SergTyapkin/Compass-Minecraft-ESP32/firmware/src/clocks.h

#pragma once
#include "pixel.h"

#define CL_BLUE 0     // Светлое небо
#define CL_BLUE_D 1   // Темное небо
#define CL_YELLOW 2   // Светлая часть стрелки солнца
#define CL_YELLOW_D 3 // Темная часть стрелки солнца
#define CL_WHITE 4    // Светлая часть стрелки луны
#define CL_WHITE_D 5  // Темная часть стрелки луны

static const Pix CL_0[] = {
    {CL_WHITE, 11},
    {CL_WHITE, 19},
    {CL_WHITE, 27},
    {CL_WHITE, 35},
    {CL_WHITE, 43},
    {CL_WHITE_D, 18},
    {CL_WHITE_D, 10},
    {CL_WHITE_D, 3},
    {CL_WHITE_D, 12},
    {CL_WHITE_D, 20},
    {CL_BLUE, 48},
    {CL_BLUE, 49},
    {CL_BLUE, 50},
    {CL_BLUE, 51},
    {CL_BLUE, 52},
    {CL_BLUE, 53},
    {CL_BLUE, 54},
    {CL_BLUE_D, 40},
    {CL_BLUE_D, 41},
    {CL_BLUE_D, 42},
    {CL_BLUE_D, 44},
    {CL_BLUE_D, 45},
    {CL_BLUE_D, 46},
};
static const Pix CL_1[] = {
    {CL_WHITE, 12},
    {CL_WHITE, 20},
    {CL_WHITE, 28},
    {CL_WHITE, 35},
    {CL_WHITE, 43},
    {CL_WHITE_D, 27},
    {CL_WHITE_D, 19},
    {CL_WHITE_D, 11},
    {CL_WHITE_D, 4},
    {CL_WHITE_D, 13},
    {CL_WHITE_D, 21},
    {CL_BLUE, 40},
    {CL_BLUE, 48},
    {CL_BLUE, 49},
    {CL_BLUE, 50},
    {CL_BLUE, 51},
    {CL_BLUE, 52},
    {CL_BLUE, 53},
    {CL_BLUE_D, 32},
    {CL_BLUE_D, 41},
    {CL_BLUE_D, 42},
    {CL_BLUE_D, 44},
    {CL_BLUE_D, 45},
    {CL_BLUE_D, 54},
};
static const Pix CL_2[] = {
    {CL_WHITE, 21},
    {CL_WHITE, 28},
    {CL_WHITE, 36},
    {CL_WHITE, 43},
    {CL_WHITE_D, 20},
    {CL_WHITE_D, 13},
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
    sizeof(CL_23),
    sizeof(CL_24),
    sizeof(CL_25),
    sizeof(CL_26),
    sizeof(CL_27),
};

uint8_t getClockLen(uint8_t n) {
    return CL_SZ[n] / sizeof(Pix);
}

const Pix* getClockPix(uint8_t n) {
    return CL_FRN[n];
}

const uint8_t clockAmount = sizeof(CL_SZ) / sizeof(CL_SZ[0]);
