SergTyapkin/Compass-Minecraft-ESP32/firmware/src/arrows.h

#pragma once
#include "pixel.h"

#define AR_RED 0   // Светлая часть стрелки
#define AR_RED_D 1 // Темная часть стрелки
#define AR_GRAY 2  // Центр

static const Pix AR_0[] = {
    {AR_GRAY, 19},
    {AR_GRAY, 26},
    {AR_GRAY, 28},
    {AR_RED, 27},
    {AR_RED, 35},
    {AR_RED, 43},
    {AR_RED, 51},
};
static const Pix AR_1[] = {
    {AR_GRAY, 19},
    {AR_GRAY, 26},
    {AR_GRAY, 28},
    {AR_RED_D, 43},
    {AR_RED, 27},
    {AR_RED, 35},
    {AR_RED, 42},
    {AR_RED, 50},
};
static const Pix AR_2[] = {
    {AR_GRAY, 19},
    {AR_GRAY, 20},
    {AR_GRAY, 26},
    {AR_GRAY, 28},
    {AR_RED_D, 35},
    {AR_RED_D, 50},
    {AR_RED, 27},
    {AR_RED, 34},
    {AR_RED, 42},
    {AR_RED, 49},
};
static const Pix AR_3[] = {
    {AR_GRAY, 20},
    {AR_GRAY, 28},
    {AR_RED_D, 35},
    {AR_RED_D, 42},
    {AR_RED_D, 49},
    {AR_RED, 27},
    {AR_RED, 34},
    {AR_RED, 41},
    {AR_RED, 48},
};
static const Pix AR_4[] = {
    {AR_GRAY, 20},
    {AR_GRAY, 21},
    {AR_GRAY, 28},
    {AR_RED_D, 35},
    {AR_RED_D, 42},
    {AR_RED, 27},
    {AR_RED, 34},
    {AR_RED, 40},
    {AR_RED, 41},
};
static const Pix AR_5[] = {
    {AR_GRAY, 20},
    {AR_GRAY, 21},
    {AR_GRAY, 28},
    {AR_RED_D, 26},
    {AR_RED, 27},
    {AR_RED, 33},
    {AR_RED, 34},
    {AR_RED, 40},
};
static const Pix AR_6[] = {
    {AR_GRAY, 19},
    {AR_GRAY, 28},
    {AR_GRAY, 29},
    {AR_GRAY, 35},
    {AR_RED_D, 34},
    {AR_RED, 26},
    {AR_RED, 27},
    {AR_RED, 32},
    {AR_RED, 33},
};
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
    AR_19,
    AR_20,
    AR_21,
    AR_22,
    AR_23,
    AR_24,
    AR_25,
    AR_26,
    AR_27,
};
static const uint8_t AR_SZ[] = {
    sizeof(AR_0),
    sizeof(AR_1),
    sizeof(AR_2),
    sizeof(AR_3),
    sizeof(AR_4),
    sizeof(AR_5),
    sizeof(AR_6),
    sizeof(AR_7),
    sizeof(AR_8),
    sizeof(AR_9),
    sizeof(AR_10),
    sizeof(AR_11),
    sizeof(AR_12),
    sizeof(AR_13),
    sizeof(AR_14),
    sizeof(AR_15),
    sizeof(AR_16),
    sizeof(AR_17),
    sizeof(AR_18),
    sizeof(AR_19),
    sizeof(AR_20),
    sizeof(AR_21),
    sizeof(AR_22),
    sizeof(AR_23),
    sizeof(AR_24),
    sizeof(AR_25),
    sizeof(AR_26),
    sizeof(AR_27),
};

uint8_t getArrowLen(uint8_t n) {
    return AR_SZ[n] / sizeof(Pix);
}

const Pix* getArrowPix(uint8_t n) {
    return AR_FRN[n];
}

const uint8_t arrowAmount = sizeof(AR_SZ) / sizeof(AR_SZ[0]);
