SergTyapkin/Compass-Minecraft-ESP32/firmware/src/numbers.h

#pragma once
#include <inttypes.h>

#define SPRITE_NUMBER_HEIGHT 5
#define SPRITE_NUMBER_WIDTH 3
static const uint8_t _numbers[][SPRITE_NUMBER_HEIGHT][SPRITE_NUMBER_WIDTH] = {
    {
        {1, 1, 1},
        {1, 0, 1},
        {1, 0, 1},
        {1, 0, 1},
        {1, 1, 1},
    },
    {
        {0, 1, 0},
        {0, 1, 0},
        {0, 1, 0},
        {0, 1, 0},
        {0, 1, 0},
    },
    {
        {1, 1, 1},
        {0, 0, 1},
        {1, 1, 1},
        {1, 0, 0},
        {1, 1, 1},
    },
    {
        {1, 1, 1},
        {0, 0, 1},
        {0, 1, 1},
        {0, 0, 1},
        {1, 1, 1},
    },
    {
        {1, 0, 1},
        {1, 0, 1},
        {1, 1, 1},
        {0, 0, 1},
        {0, 0, 1},
    },
    {
        {1, 1, 1},
        {1, 0, 0},
        {1, 1, 1},
        {0, 0, 1},
        {1, 1, 1},
    },
    {
        {1, 1, 1},
        {1, 0, 0},
        {1, 1, 1},
        {1, 0, 1},
        {1, 1, 1},
    },
    {
        {1, 1, 1},
        {0, 0, 1},
        {0, 0, 1},
        {0, 0, 1},
        {0, 0, 1},
    },
    {
        {1, 1, 1},
        {1, 0, 1},
        {1, 1, 1},
        {1, 0, 1},
        {1, 1, 1},
    },
    {
        {1, 1, 1},
        {1, 0, 1},
        {1, 1, 1},
        {0, 0, 1},
        {1, 1, 1},
    },
};
